haydonryan/dell-fan-proxy/Images/IMG_0835.jpg

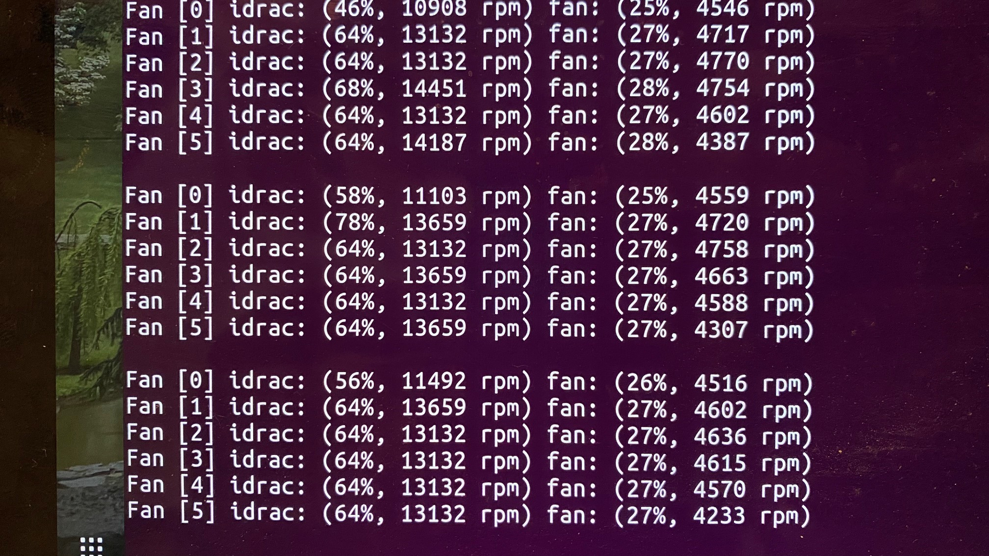
Images/IMG_0835.jpg
