haydonryan/dell-fan-proxy/Images/IMG_1567.jpg

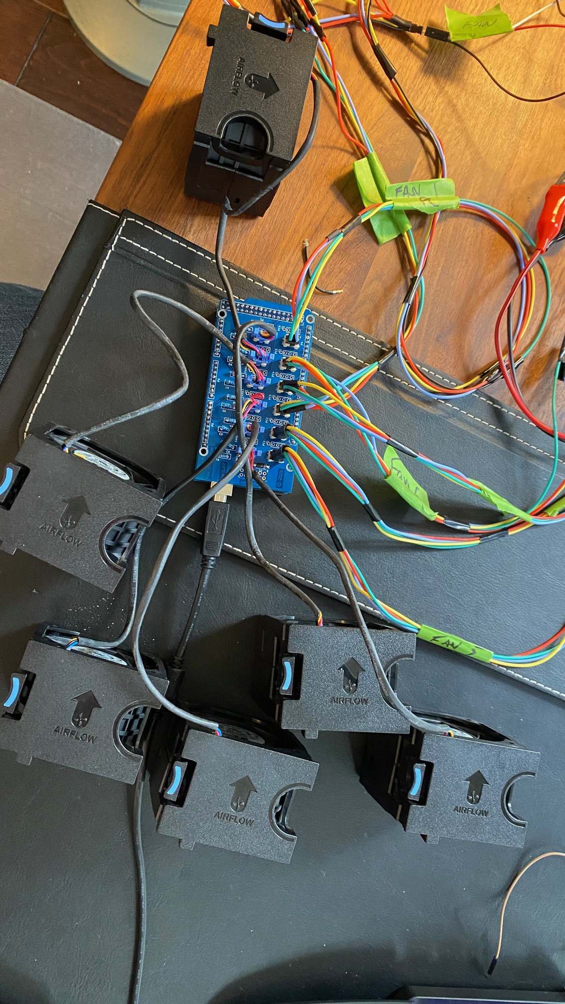
Images/IMG_1567.jpg
